MGod-monkey/ESP32-Debugger/project/CH554_Keil_proj/compound.h

/********************************** (C) COPYRIGHT *******************************
* File Name          :Compound_Dev.C											*	
* Author             : WCH                                                      *
* Version            : V1.2                                                     *
* Date               : 2017/02/24                                               *
* Description        : A demo for USB compound device created by CH554, support *
					   keyboard , and HID-compliant device.                     *
********************************************************************************/


#ifndef	__COMPOUND_H__
#define __COMPOUND_H__

// CH554 特定的类型定义
#define UINT8X __xdata unsigned char    // xdata 存储类型
#define UINT8I __idata unsigned char    // idata 存储类型
#define UINT8C __code unsigned char     // code 存储类型
#define UINT16X __xdata unsigned short  // xdata 16位
#define UINT16I __idata unsigned short  // idata 16位
#define UINT32 unsigned long
#define PUINT8 unsigned char *

extern UINT8I 	UsbConfig;	
extern UINT16  TouchKeyButton;
extern UINT8I Endp1Busy;
extern UINT8I USBD0;
extern UINT8I USBByteCount;
extern UINT8I USBBufOutPoint;
extern UINT8I UartByteCount;
extern UINT8I Uart_Input_Point;
extern UINT8I Uart_Output_Point;
extern UINT8X  Ep2Buffer[2*64]; 
extern UINT8X  Ep3Buffer[64];  
extern UINT8X  Ep3Buffer2[64]; 
extern UINT8I Endp2Busy;
extern UINT8  USB_RequestFlag;

extern	void 	USBDeviceInit();
extern	void 	HIDValueHandle();
	
#endif
/**************************** END *************************************/
